kzmijews/8bit-comp/design/clock/schema/ne555n-astable.png

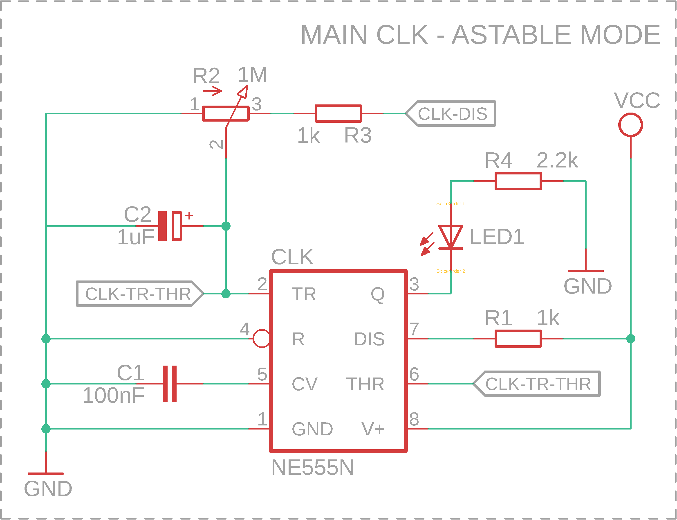
design/clock/schema/ne555n-astable.png
