kzmijews/8bit-comp/design/display/imgs/display-decode-array.png

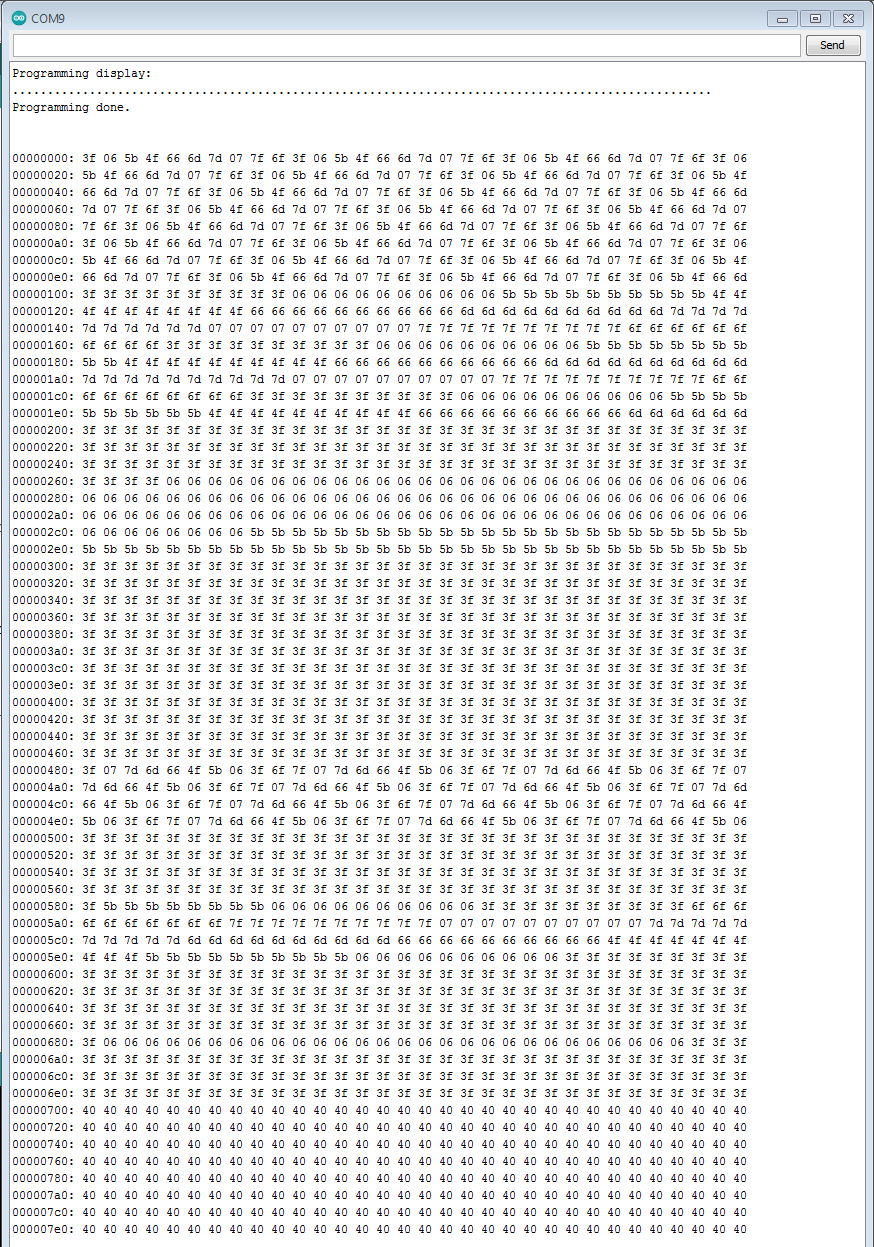
design/display/imgs/display-decode-array.png
