kzmijews/8bit-comp/rel-8bit-computer.pdf

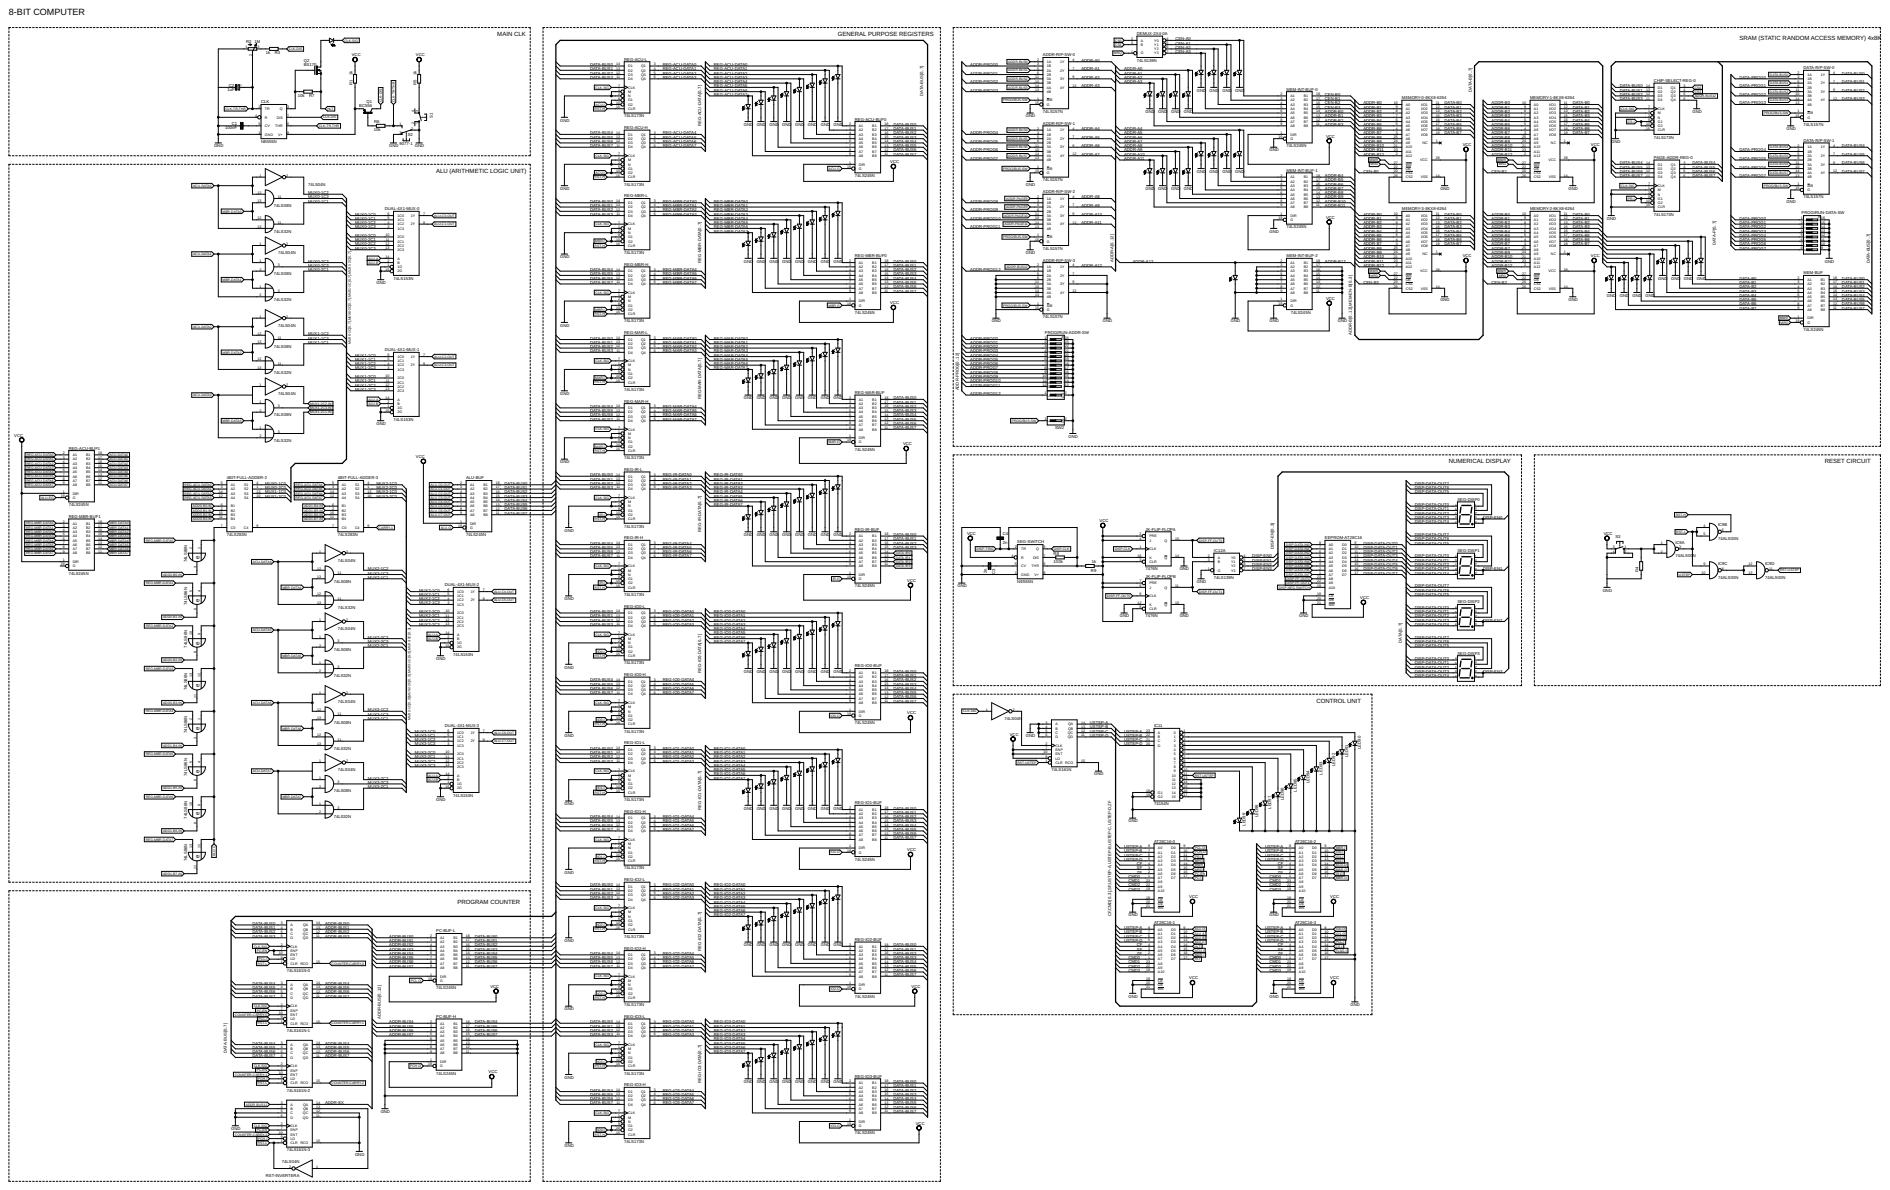
[picture p22: page 1]

SRAM (STATIC RANDOM ACCESS MEMORY) 4x8K

GND GND

GND GND GND GND

ALU (ARITHMETIC LOGIC UNIT)

PROG/RUN-DATA-SW

REG-MBR-DATA[0..7] REG-M

AR-DATA[0..7] REG-IR-DATA[0..7] REG-IO0-DATA[0..7] REG-IO1-DATA[0..7] REG-IO2-DATA[0..7] REG-IO3-DATA[0..7]

REG-ACU-DATA0
REG-ACU-DATA1
REG-ACU-DATA2
REG-ACU-DATA3
REG-ACU-DATA4
REG-ACU-DATA5
REG-ACU-DATA6
REG-ACU-DATA7

ALU-C7-OUT ALU-EO

REG-MBR-DATA0
REG-MBR-DATA1
REG-MBR-DATA2
REG-MBR-DATA3

DISP-DATA-IN0 DISP-DATA-IN1 DISP-DATA-IN2 DISP-DATA-IN3 DISP-DATA-IN4 DISP-DATA-IN5 DISP-DATA-IN6 DISP-DATA-IN7

DATA-IR0 DATA-IR1 DATA-IR2 DATA-IR3

CF,CMD[0..3],SF,USTEP-A,USTEP-B,USTEP-C,USTEP-D,ZF
