kzmijews/8bit-comp/design/ram/schema/rel-ram-8x2K.pdf

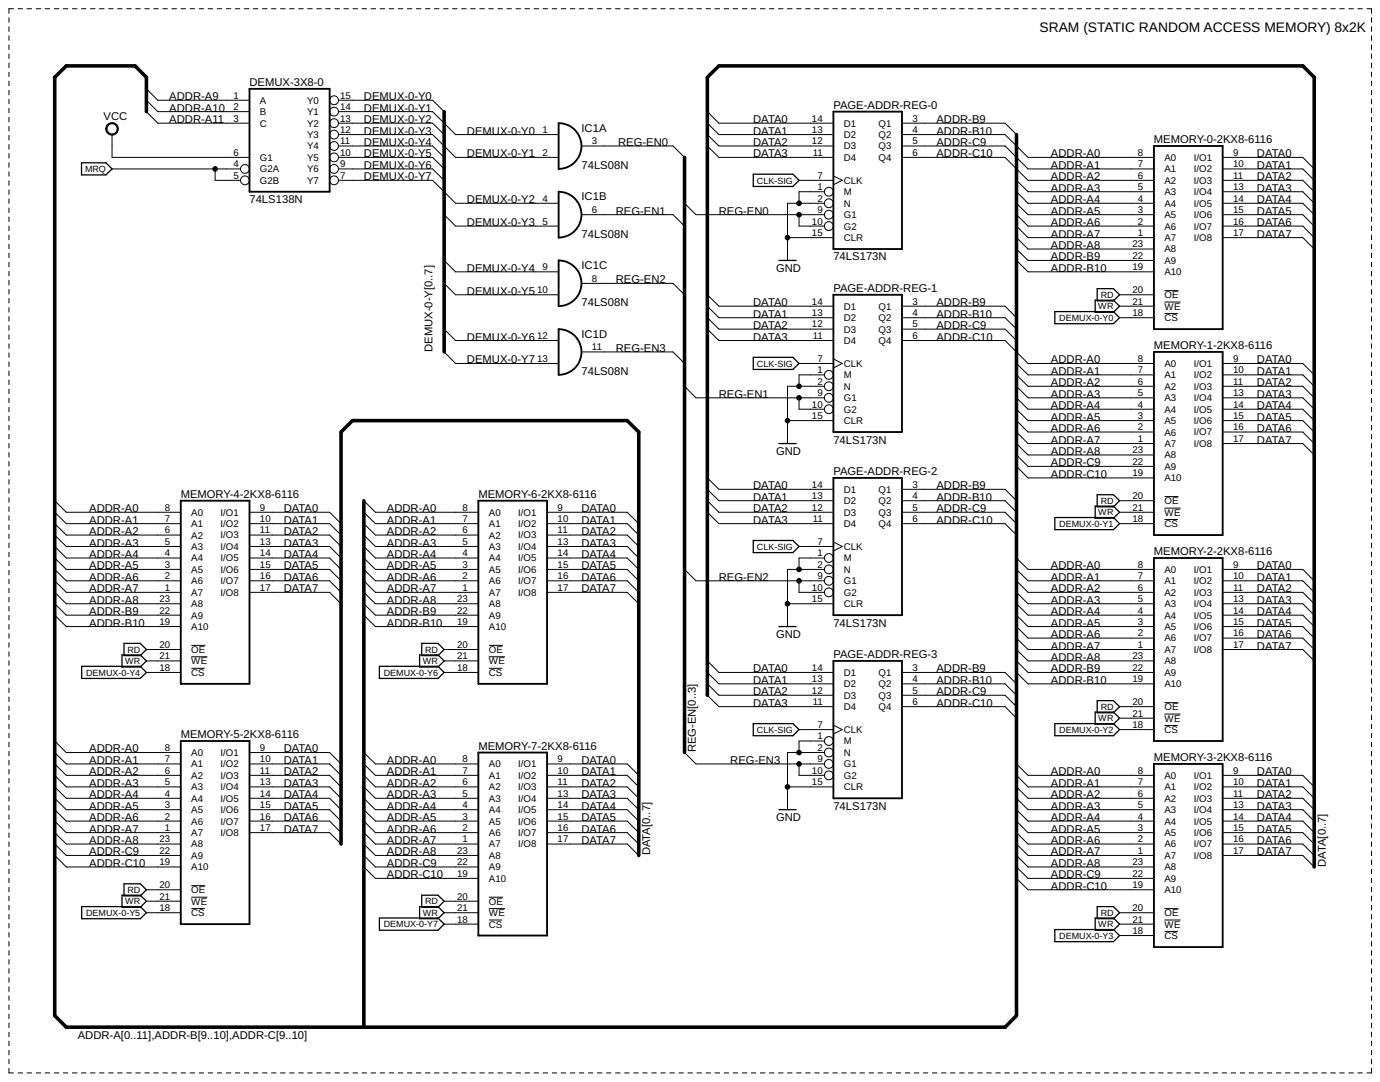
[picture p35: page 1]

SRAM (STATIC RANDOM ACCESS MEMORY) 8x2K
