kzmijews/8bit-comp/design/clock/ltspice/ne555n-monostable-debouncing/ne555n-monostable-debouncing.asc

A1: srflop; Vhigh=4.9V Vlow=0V
C3: cap; 0.1µ; V=10 Irms=2.4 Rser=0.0421193 Lser=0
C4: cap; 10n
D1: LED; NSSW008CT-P1
Q1: npn
R5: res; 100R
R6: res; 1K
R6: res; 2R
R7: res; 1000K
Rt1: res; 5K
Rt2: res; 5K
Rt3: res; 5K
S1: sw
U1: LT1720
U2: LT1720
V1: voltage; 5
V2: voltage; PULSE(0 5 0.1 0 0.01 0.01 0.01 2)
Named nets: 0, THR, Q, set, reset, TRG, CTRL
.tran 1
.model SW SW(RON=.1 ROFF=1GIG VT=4)
DBG_BUTTOM
STEPPING CLK
