kzmijews/8bit-comp/ltspice/debouncing_circuit_timer555_monostable/debouncing_circuit_timer555_monostable.asc

A1: srflop; Vhigh=5V Vlow=0V
C1: cap; 0.1µ; V=10 Irms=2.4 Rser=0.0421193 Lser=0
C2: cap; 10n
D1: LED; NSSW008CT-P1
Q1: npn
R1: res; 5K
R2: res; 5K
R3: res; 5K
R4: res; 1000K
R5: res; 1K
R6: res; 2R
R7: res; 100R
S1: sw
U1: LT1720
U2: LT1720
V1: voltage; 5
V2: voltage; PULSE(0 5 0.1 0 0 0.01)
Named nets: 0, THR, Q, set, reset, TRG, CTRL
.tran 1
.model SW SW(RON=.1 ROFF=1GIG VT=4)
