kzmijews/8bit-comp/design/alu/schema/rel-2b-alu.sch

## EAGLE design design/alu/schema/rel-2b-alu.sch (2024-04-11)

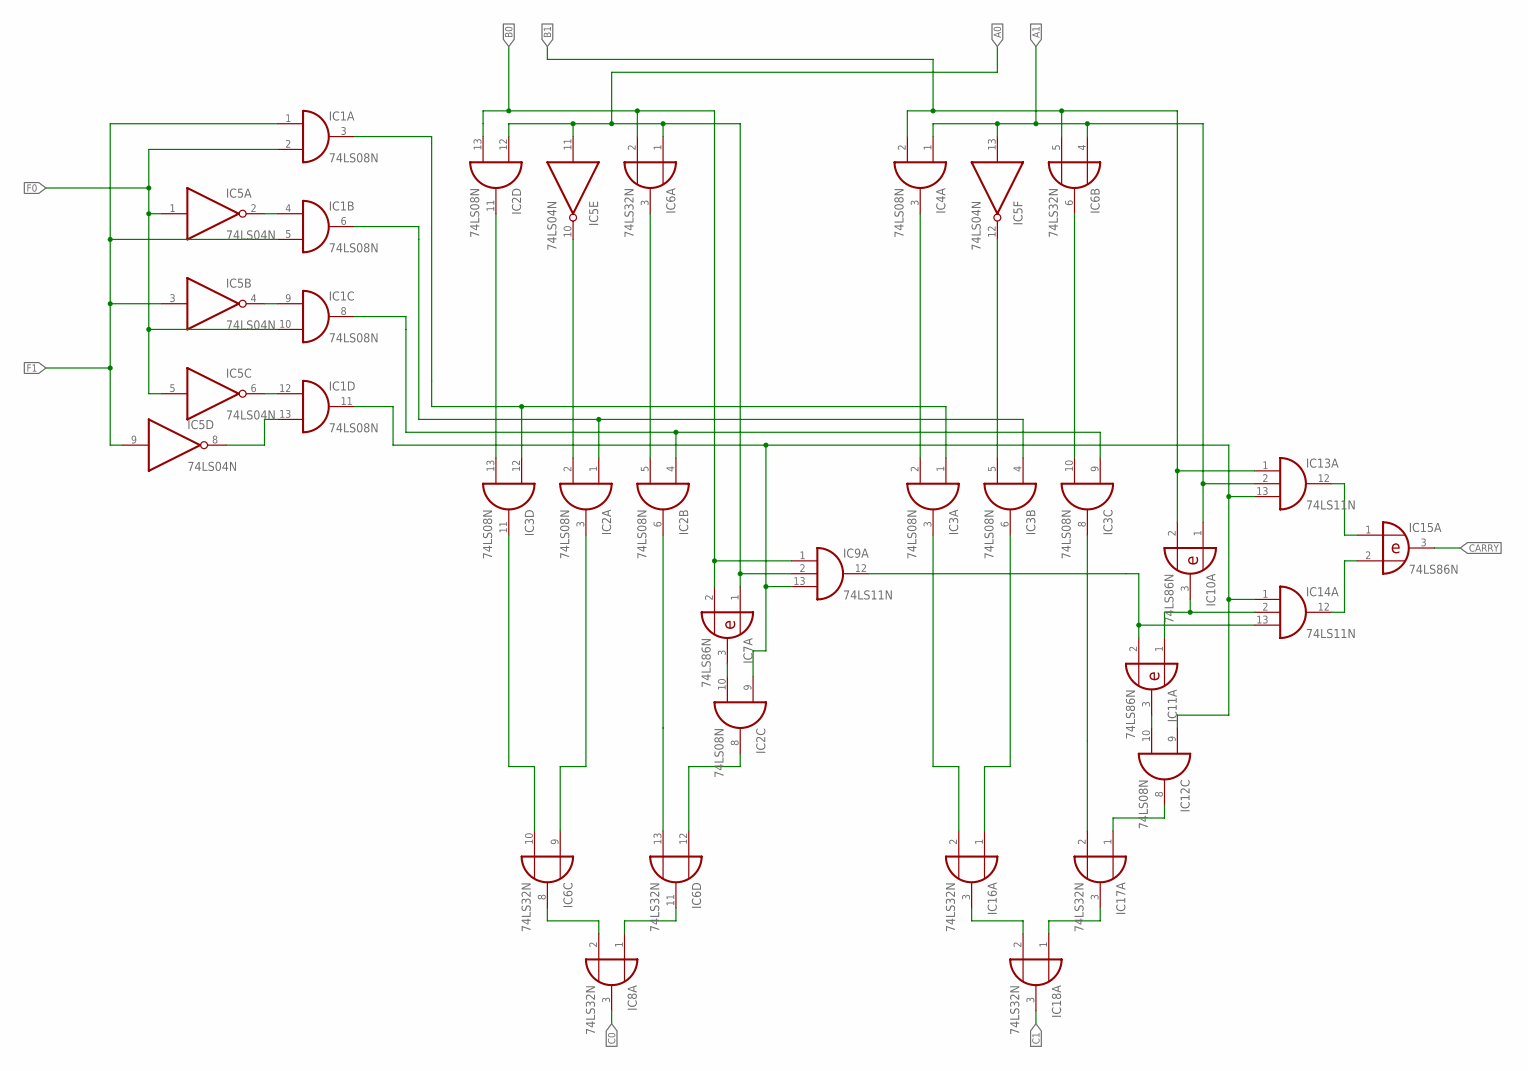
[picture p43: schematic rel-2b-alu.sch]

Parts:
IC1, IC2, IC3, IC4, IC12: 74LS08N; DIL14
IC5: 74LS04N; DIL14
IC6, IC8, IC16, IC17, IC18: 74LS32N; DIL14
IC7, IC10, IC11, IC15: 74LS86N; DIL14
IC9, IC13, IC14: 74LS11N; DIL14

Connections:
A0: IC2.12 (I0), IC5.11 (I), IC6.1 (I0), IC7.1 (I0), IC9.2 (I1)
A1: IC4.1 (I0), IC5.13 (I), IC6.4 (I0), IC10.1 (I0), IC13.2 (I1)
B0: IC2.13 (I1), IC6.2 (I1), IC7.2 (I1), IC9.1 (I0)
B1: IC4.2 (I1), IC6.5 (I1), IC10.2 (I1), IC13.1 (I0)
C0: IC8.3 (O)
C1: IC18.3 (O)
CARRY: IC15.3 (O)
F0: IC1.2 (I1), IC1.10 (I1), IC5.1 (I), IC5.5 (I)
F1: IC1.1 (I0), IC1.5 (I1), IC5.3 (I), IC5.9 (I)
unnamed: IC1.4 (I0), IC5.2 (O)
unnamed: IC1.9 (I0), IC5.4 (O)
unnamed: IC1.12 (I0), IC5.6 (O)
unnamed: IC1.3 (O), IC3.1 (I0), IC3.12 (I0)
unnamed: IC1.6 (O), IC2.1 (I0), IC3.4 (I0)
unnamed: IC1.13 (I1), IC5.8 (O)
unnamed: IC1.8 (O), IC2.4 (I0), IC3.9 (I0)
unnamed: IC1.11 (O), IC2.9 (I0), IC9.13 (I2), IC12.9 (I0), IC13.13 (I2), IC14.1 (I0)
unnamed: IC2.11 (O), IC3.13 (I1)
unnamed: IC2.2 (I1), IC5.10 (O)
unnamed: IC2.5 (I1), IC6.3 (O)
unnamed: IC3.2 (I1), IC4.3 (O)
unnamed: IC3.5 (I1), IC5.12 (O)
unnamed: IC3.10 (I1), IC6.6 (O)
unnamed: IC2.10 (I1), IC7.3 (O)
unnamed: IC3.11 (O), IC6.10 (I1)
unnamed: IC2.3 (O), IC6.9 (I0)
unnamed: IC2.6 (O), IC6.13 (I1)
unnamed: IC2.8 (O), IC6.12 (I0)
unnamed: IC6.8 (O), IC8.2 (I1)
unnamed: IC6.11 (O), IC8.1 (I0)
unnamed: IC10.3 (O), IC11.1 (I0), IC14.2 (I1)
unnamed: IC9.12 (O), IC11.2 (I1), IC14.13 (I2)
unnamed: IC3.3 (O), IC16.2 (I1)
unnamed: IC3.6 (O), IC16.1 (I0)
unnamed: IC3.8 (O), IC17.2 (I1)
unnamed: IC11.3 (O), IC12.10 (I1)
unnamed: IC13.12 (O), IC15.1 (I0)
unnamed: IC14.12 (O), IC15.2 (I1)
unnamed: IC12.8 (O), IC17.1 (I0)
unnamed: IC16.3 (O), IC18.2 (I1)
unnamed: IC17.3 (O), IC18.1 (I0)
