kzmijews/8bit-comp/design/alu/schema/rel-alu.sch

## EAGLE design design/alu/schema/rel-alu.sch (2024-11-08)

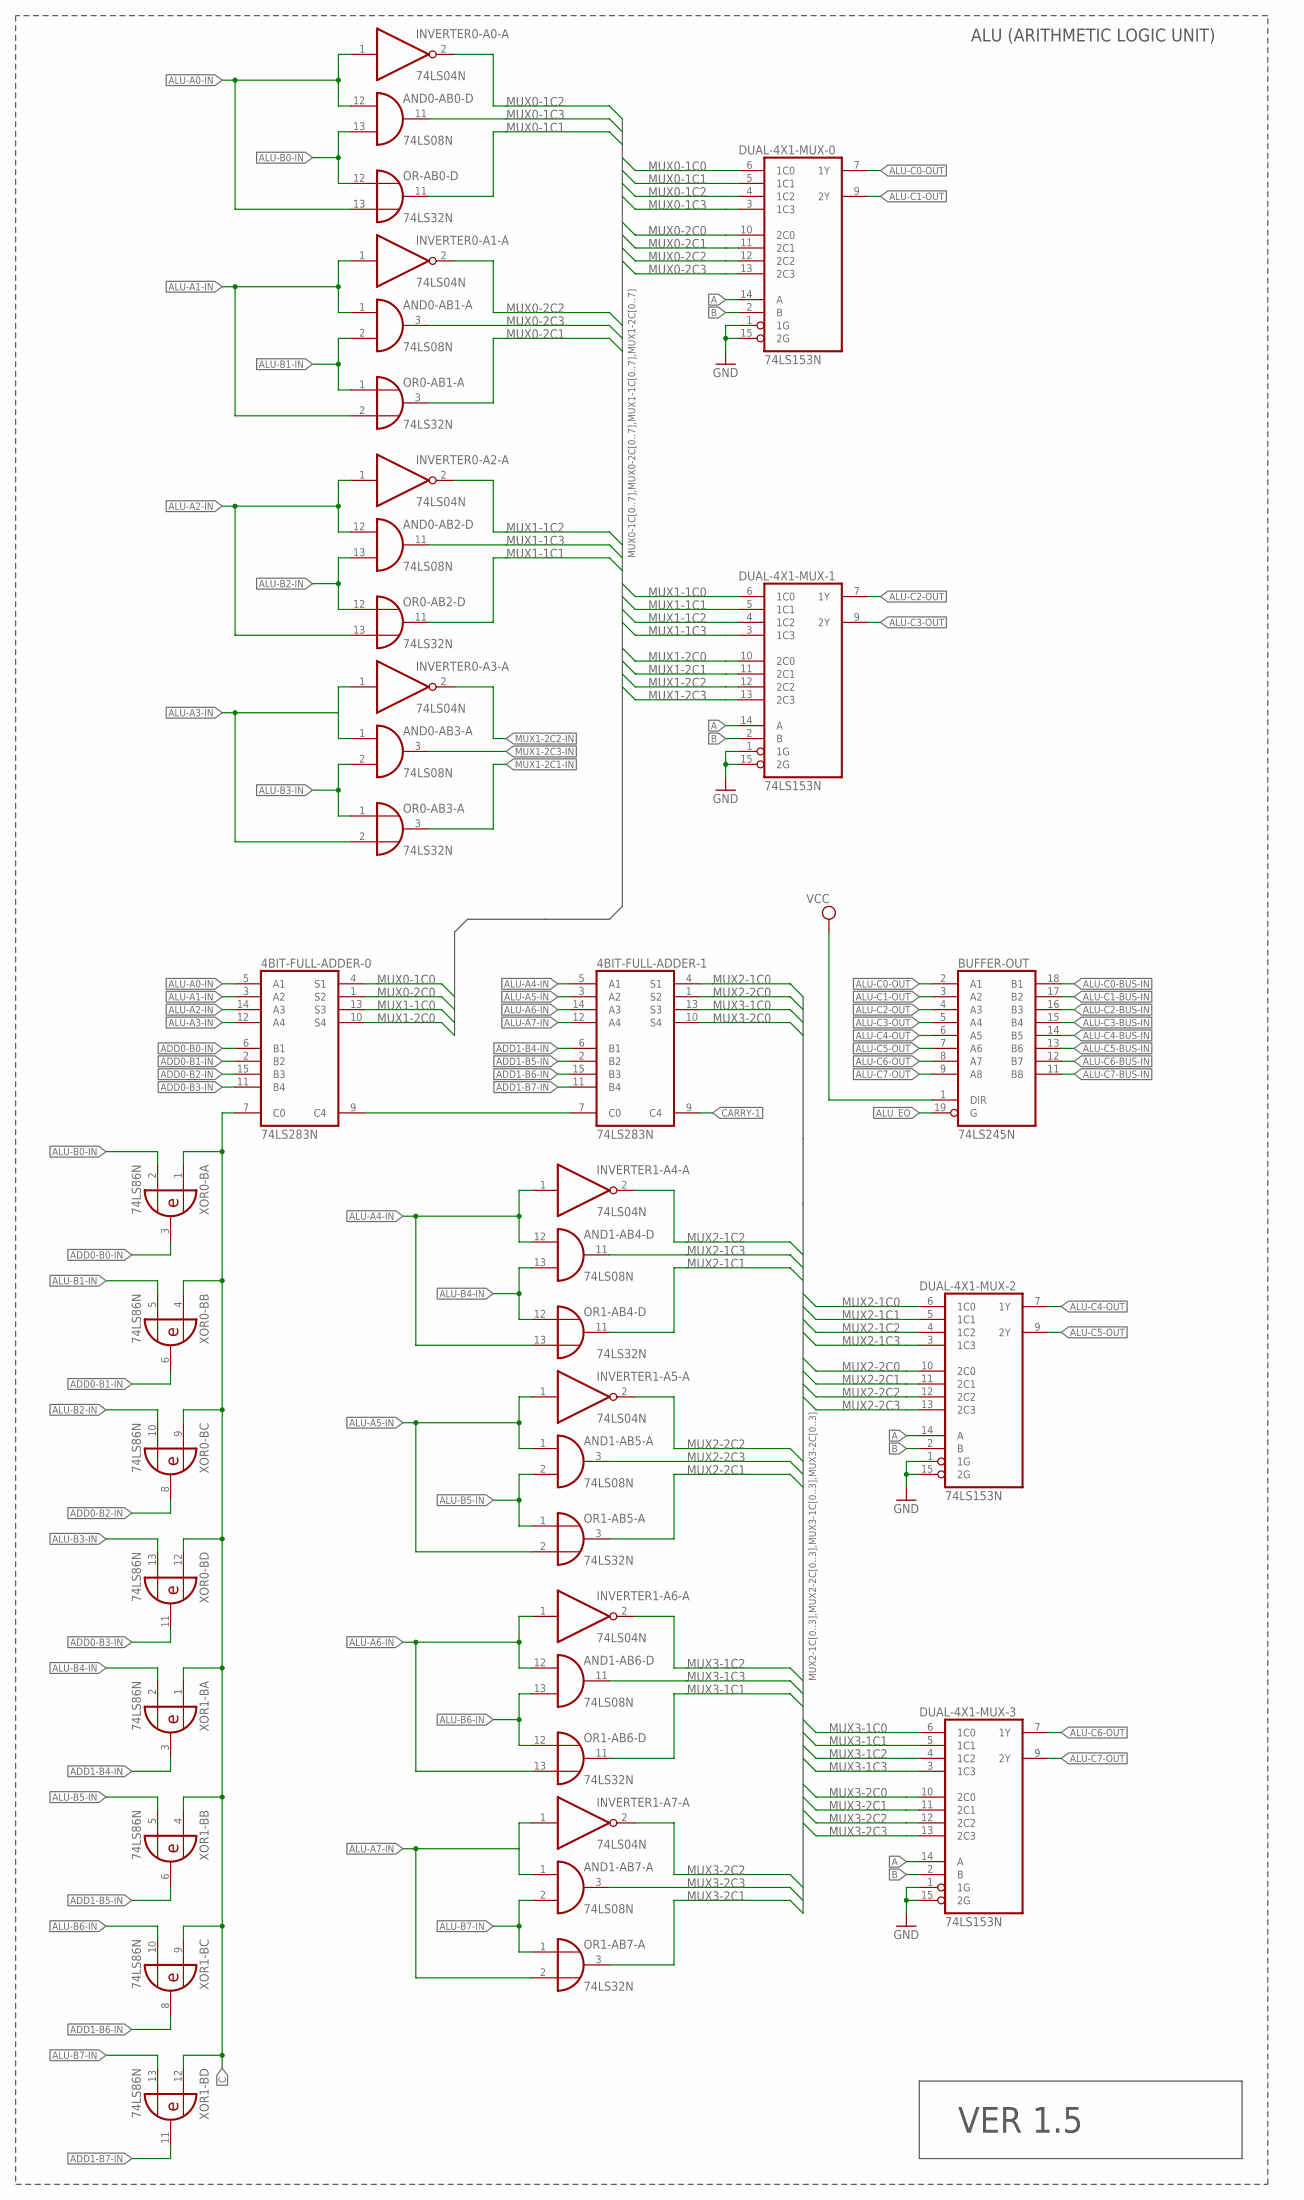
[picture p44: schematic rel-alu.sch]

Parts:
4BIT-FULL-ADDER-0, 4BIT-FULL-ADDER-1: 74LS283N; DIL16
AND0-AB0-, AND0-AB1-, AND0-AB2-, AND0-AB3-, AND1-AB4-, AND1-AB5-, AND1-AB6-, AND1-AB7-: 74LS08N; DIL14
BUFFER-OUT: 74LS245N; DIL20
DUAL-4X1-MUX-0, DUAL-4X1-MUX-1, DUAL-4X1-MUX-2, DUAL-4X1-MUX-3: 74LS153N; DIL16
INVERTER0-A0-, INVERTER0-A1-, INVERTER0-A2-, INVERTER0-A3-, INVERTER1-A4-, INVERTER1-A5-, INVERTER1-A6-, INVERTER1-A7-: 74LS04N; DIL14
OR0-AB1-, OR0-AB2-, OR0-AB3-, OR1-AB4-, OR1-AB5-, OR1-AB6-, OR1-AB7-: 74LS32N; DIL14
OR-AB0-: 74LS32N; DIL14
XOR0-B, XOR1-B: 74LS86N; DIL14

Connections:
A: DUAL-4X1-MUX-0.14 (A), DUAL-4X1-MUX-1.14 (A), DUAL-4X1-MUX-2.14 (A), DUAL-4X1-MUX-3.14 (A)
ADD0-B0-IN: 4BIT-FULL-ADDER-0.6 (B1), XOR0-B.3 (O)
ADD0-B1-IN: 4BIT-FULL-ADDER-0.2 (B2), XOR0-B.6 (O)
ADD0-B2-IN: 4BIT-FULL-ADDER-0.15 (B3), XOR0-B.8 (O)
ADD0-B3-IN: 4BIT-FULL-ADDER-0.11 (B4), XOR0-B.11 (O)
ADD1-B4-IN: 4BIT-FULL-ADDER-1.6 (B1), XOR1-B.3 (O)
ADD1-B5-IN: 4BIT-FULL-ADDER-1.2 (B2), XOR1-B.6 (O)
ADD1-B6-IN: 4BIT-FULL-ADDER-1.15 (B3), XOR1-B.8 (O)
ADD1-B7-IN: 4BIT-FULL-ADDER-1.11 (B4), XOR1-B.11 (O)
ALU-A0-IN: 4BIT-FULL-ADDER-0.5 (A1), AND0-AB0-.12 (I0), INVERTER0-A0-.1 (I), OR-AB0-.13 (I1)
ALU-A1-IN: 4BIT-FULL-ADDER-0.3 (A2), AND0-AB1-.1 (I0), INVERTER0-A1-.1 (I), OR0-AB1-.2 (I1)
ALU-A2-IN: 4BIT-FULL-ADDER-0.14 (A3), AND0-AB2-.12 (I0), INVERTER0-A2-.1 (I), OR0-AB2-.13 (I1)
ALU-A3-IN: 4BIT-FULL-ADDER-0.12 (A4), AND0-AB3-.1 (I0), INVERTER0-A3-.1 (I), OR0-AB3-.2 (I1)
ALU-A4-IN: 4BIT-FULL-ADDER-1.5 (A1), AND1-AB4-.12 (I0), INVERTER1-A4-.1 (I), OR1-AB4-.13 (I1)
ALU-A5-IN: 4BIT-FULL-ADDER-1.3 (A2), AND1-AB5-.1 (I0), INVERTER1-A5-.1 (I), OR1-AB5-.2 (I1)
ALU-A6-IN: 4BIT-FULL-ADDER-1.14 (A3), AND1-AB6-.12 (I0), INVERTER1-A6-.1 (I), OR1-AB6-.13 (I1)
ALU-A7-IN: 4BIT-FULL-ADDER-1.12 (A4), AND1-AB7-.1 (I0), INVERTER1-A7-.1 (I), OR1-AB7-.2 (I1)
ALU-B0-IN: AND0-AB0-.13 (I1), OR-AB0-.12 (I0), XOR0-B.2 (I1)
ALU-B1-IN: AND0-AB1-.2 (I1), OR0-AB1-.1 (I0), XOR0-B.5 (I1)
ALU-B2-IN: AND0-AB2-.13 (I1), OR0-AB2-.12 (I0), XOR0-B.10 (I1)
ALU-B3-IN: AND0-AB3-.2 (I1), OR0-AB3-.1 (I0), XOR0-B.13 (I1)
ALU-B4-IN: AND1-AB4-.13 (I1), OR1-AB4-.12 (I0), XOR1-B.2 (I1)
ALU-B5-IN: AND1-AB5-.2 (I1), OR1-AB5-.1 (I0), XOR1-B.5 (I1)
ALU-B6-IN: AND1-AB6-.13 (I1), OR1-AB6-.12 (I0), XOR1-B.10 (I1)
ALU-B7-IN: AND1-AB7-.2 (I1), OR1-AB7-.1 (I0), XOR1-B.13 (I1)
ALU-C0-BUS-IN: BUFFER-OUT.18 (B1)
ALU-C0-OUT: BUFFER-OUT.2 (A1), DUAL-4X1-MUX-0.7 (1Y)
ALU-C1-BUS-IN: BUFFER-OUT.17 (B2)
ALU-C1-OUT: BUFFER-OUT.3 (A2), DUAL-4X1-MUX-0.9 (2Y)
ALU-C2-BUS-IN: BUFFER-OUT.16 (B3)
ALU-C2-OUT: BUFFER-OUT.4 (A3), DUAL-4X1-MUX-1.7 (1Y)
ALU-C3-BUS-IN: BUFFER-OUT.15 (B4)
ALU-C3-OUT: BUFFER-OUT.5 (A4), DUAL-4X1-MUX-1.9 (2Y)
ALU-C4-BUS-IN: BUFFER-OUT.14 (B5)
ALU-C4-OUT: BUFFER-OUT.6 (A5), DUAL-4X1-MUX-2.7 (1Y)
ALU-C5-BUS-IN: BUFFER-OUT.13 (B6)
ALU-C5-OUT: BUFFER-OUT.7 (A6), DUAL-4X1-MUX-2.9 (2Y)
ALU-C6-BUS-IN: BUFFER-OUT.12 (B7)
ALU-C6-OUT: BUFFER-OUT.8 (A7), DUAL-4X1-MUX-3.7 (1Y)
ALU-C7-BUS-IN: BUFFER-OUT.11 (B8)
ALU-C7-OUT: BUFFER-OUT.9 (A8), DUAL-4X1-MUX-3.9 (2Y)
ALU_EO: BUFFER-OUT.19 (G)
B: DUAL-4X1-MUX-0.2 (B), DUAL-4X1-MUX-1.2 (B), DUAL-4X1-MUX-2.2 (B), DUAL-4X1-MUX-3.2 (B)
C: 4BIT-FULL-ADDER-0.7 (C0), XOR0-B.1 (I0), XOR0-B.4 (I0), XOR0-B.9 (I0), XOR0-B.12 (I0), XOR1-B.1 (I0), XOR1-B.4 (I0), XOR1-B.9 (I0), XOR1-B.12 (I0)
CARRY-1: 4BIT-FULL-ADDER-1.9 (C4)
GND: DUAL-4X1-MUX-0.1 (1G), DUAL-4X1-MUX-0.15 (2G), DUAL-4X1-MUX-1.1 (1G), DUAL-4X1-MUX-1.15 (2G), DUAL-4X1-MUX-2.1 (1G), DUAL-4X1-MUX-2.15 (2G), DUAL-4X1-MUX-3.1 (1G), DUAL-4X1-MUX-3.15 (2G)
MUX0-1C0: 4BIT-FULL-ADDER-0.4 (S1), DUAL-4X1-MUX-0.6 (1C0)
MUX0-1C1: DUAL-4X1-MUX-0.5 (1C1), OR-AB0-.11 (O)
MUX0-1C2: DUAL-4X1-MUX-0.4 (1C2), INVERTER0-A0-.2 (O)
MUX0-1C3: AND0-AB0-.11 (O), DUAL-4X1-MUX-0.3 (1C3)
MUX0-2C0: 4BIT-FULL-ADDER-0.1 (S2), DUAL-4X1-MUX-0.10 (2C0)
MUX0-2C1: DUAL-4X1-MUX-0.11 (2C1), OR0-AB1-.3 (O)
MUX0-2C2: DUAL-4X1-MUX-0.12 (2C2), INVERTER0-A1-.2 (O)
MUX0-2C3: AND0-AB1-.3 (O), DUAL-4X1-MUX-0.13 (2C3)
MUX1-1C0: 4BIT-FULL-ADDER-0.13 (S3), DUAL-4X1-MUX-1.6 (1C0)
MUX1-1C1: DUAL-4X1-MUX-1.5 (1C1), OR0-AB2-.11 (O)
MUX1-1C2: DUAL-4X1-MUX-1.4 (1C2), INVERTER0-A2-.2 (O)
MUX1-1C3: AND0-AB2-.11 (O), DUAL-4X1-MUX-1.3 (1C3)
MUX1-2C0: 4BIT-FULL-ADDER-0.10 (S4), DUAL-4X1-MUX-1.10 (2C0)
MUX1-2C1: DUAL-4X1-MUX-1.11 (2C1)
MUX1-2C1-IN: OR0-AB3-.3 (O)
MUX1-2C2: DUAL-4X1-MUX-1.12 (2C2)
MUX1-2C2-IN: INVERTER0-A3-.2 (O)
MUX1-2C3: DUAL-4X1-MUX-1.13 (2C3)
MUX1-2C3-IN: AND0-AB3-.3 (O)
MUX2-1C0: 4BIT-FULL-ADDER-1.4 (S1), DUAL-4X1-MUX-2.6 (1C0)
MUX2-1C1: DUAL-4X1-MUX-2.5 (1C1), OR1-AB4-.11 (O)
MUX2-1C2: DUAL-4X1-MUX-2.4 (1C2), INVERTER1-A4-.2 (O)
MUX2-1C3: AND1-AB4-.11 (O), DUAL-4X1-MUX-2.3 (1C3)
MUX2-2C0: 4BIT-FULL-ADDER-1.1 (S2), DUAL-4X1-MUX-2.10 (2C0)
MUX2-2C1: DUAL-4X1-MUX-2.11 (2C1), OR1-AB5-.3 (O)
MUX2-2C2: DUAL-4X1-MUX-2.12 (2C2), INVERTER1-A5-.2 (O)
MUX2-2C3: AND1-AB5-.3 (O), DUAL-4X1-MUX-2.13 (2C3)
MUX3-1C0: 4BIT-FULL-ADDER-1.13 (S3), DUAL-4X1-MUX-3.6 (1C0)
MUX3-1C1: DUAL-4X1-MUX-3.5 (1C1), OR1-AB6-.11 (O)
MUX3-1C2: DUAL-4X1-MUX-3.4 (1C2), INVERTER1-A6-.2 (O)
MUX3-1C3: AND1-AB6-.11 (O), DUAL-4X1-MUX-3.3 (1C3)
MUX3-2C0: 4BIT-FULL-ADDER-1.10 (S4), DUAL-4X1-MUX-3.10 (2C0)
MUX3-2C1: DUAL-4X1-MUX-3.11 (2C1), OR1-AB7-.3 (O)
MUX3-2C2: DUAL-4X1-MUX-3.12 (2C2), INVERTER1-A7-.2 (O)
MUX3-2C3: AND1-AB7-.3 (O), DUAL-4X1-MUX-3.13 (2C3)
unnamed: 4BIT-FULL-ADDER-0.9 (C4), 4BIT-FULL-ADDER-1.7 (C0)
VCC: BUFFER-OUT.1 (DIR)

Notes on the sheet:
ALU (ARITHMETIC LOGIC UNIT)
VER 1.5
