kzmijews/8bit-comp/design/clock/schema/ne555n-astable.sch

## EAGLE design design/clock/schema/ne555n-astable.sch (2023-10-19)

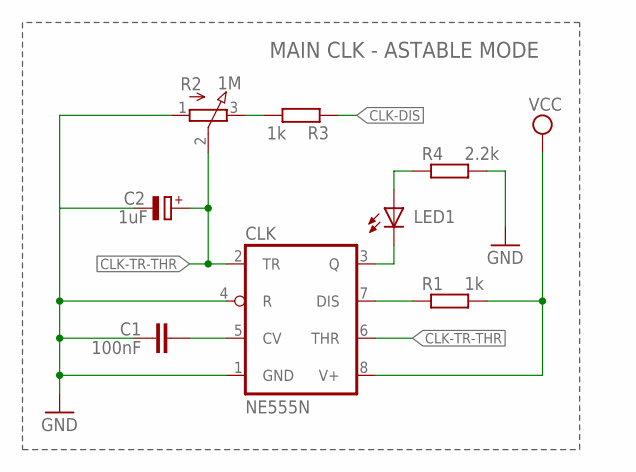
[picture p45: schematic ne555n-astable.sch]

Parts:
C1: 100nF; C025-050X050
C2: 1uF; E2-5
CLK: NE555N; DIL08
LED1: LED_ELD260; LED_LD260
R1, R3: 1k; 0204/5
R2: 1M; 3RP/1610N
R4: 2.2k; 0204/5

Connections:
CLK-CV: C1.2, CLK.5 (CV)
CLK-DIS: CLK.7 (DIS), R1.1, R3.1
CLK-Q: CLK.3 (Q), LED1.K (C)
CLK-TR-THR: C2.+, CLK.2 (TR), CLK.6 (THR), R2.2 (S)
GND: C1.1, C2.-, CLK.1 (GND), CLK.4 (R), R2.1 (A), R4.2
unnamed: R2.3 (E), R3.2
unnamed: LED1.A, R4.1
VCC: CLK.8 (V+), R1.2

Notes on the sheet:
MAIN CLK - ASTABLE MODE
