kzmijews/8bit-comp/design/clock/schema/ne555n-monostable.sch

## EAGLE design design/clock/schema/ne555n-monostable.sch (2023-10-19)

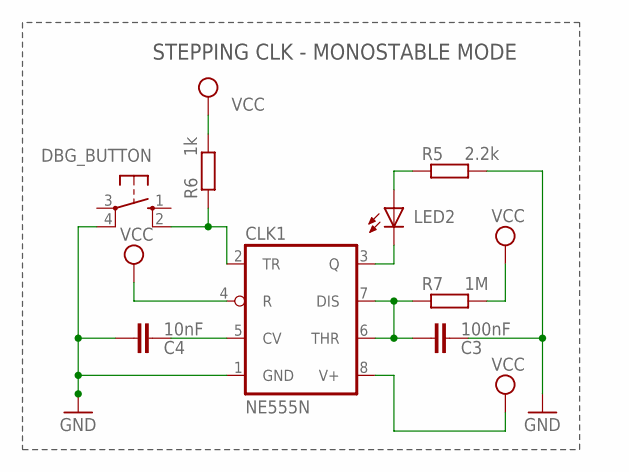
[picture p46: schematic ne555n-monostable.sch]

Parts:
C3: 100nF; C025-050X050
C4: 10nF; C025-050X050
CLK1: NE555N; DIL08
DBG_BUTTON: 10-XX; B3F-10XX
LED2: LED_ELD260; LED_LD260
R5: 2.2k; 0204/5
R6: 1k; 0204/5
R7: 1M; 0204/5

Connections:
GND: C3.1, C4.2, CLK1.1 (GND), DBG_BUTTON.4 (P1), R5.2
unnamed: CLK1.3 (Q), LED2.K (C)
unnamed: LED2.A, R5.1
unnamed: CLK1.2 (TR), DBG_BUTTON.2 (S1), R6.1
unnamed: C3.2, CLK1.6 (THR), CLK1.7 (DIS), R7.1
unnamed: C4.1, CLK1.5 (CV)
VCC: CLK1.4 (R), CLK1.8 (V+), R6.2, R7.2

Notes on the sheet:
STEPPING CLK - MONOSTABLE MODE
