kzmijews/8bit-comp/design/clock/schema/rel-clock.sch

## EAGLE design design/clock/schema/rel-clock.sch (2024-07-01)

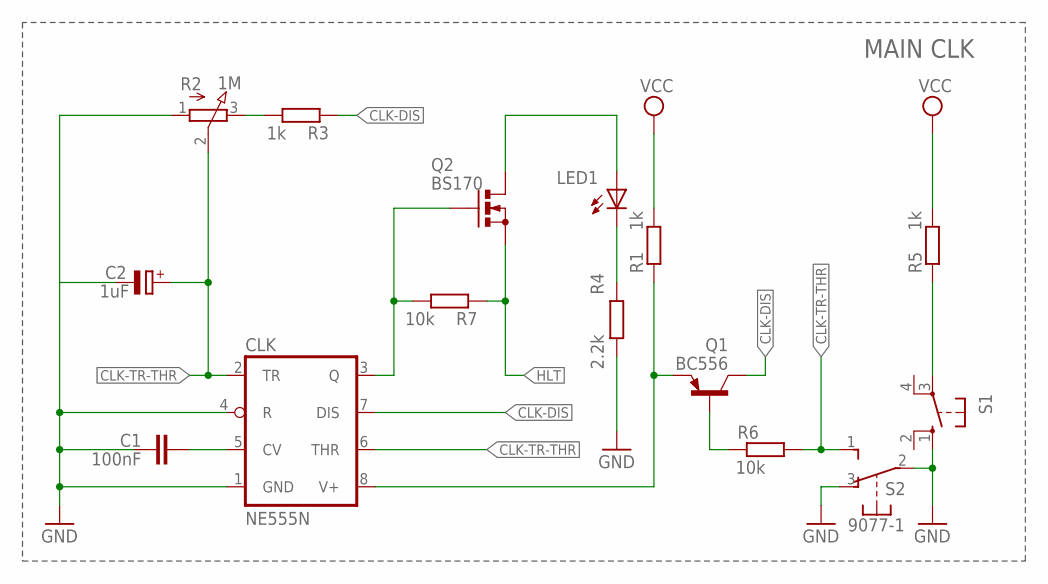
[picture p47: schematic rel-clock.sch]

Parts:
C1: 100nF; C025-050X050
C2: 1uF; E2-5
CLK: NE555N; DIL08
LED1: LED_ELD260; LED_LD260
Q1: BC556; TO92-EBC
Q2: BS170; SOT54E
R1, R3, R5: 1k; 0204/5
R2: 1M; 3RP/1610N
R4: 2.2k; 0204/5
R6, R7: 10k; 0204/5
S1: 10-XX; B3F-10XX
S2: 9077-1

Connections:
CLK-CV: C1.2, CLK.5 (CV)
CLK-DIS: CLK.7 (DIS), Q1.C, R3.1
CLK-TR-THR: C2.+, CLK.2 (TR), CLK.6 (THR), Q1.B, R2.2 (S), R6.1, R6.2, S2.1 (S)
GND: C1.1, C2.-, CLK.1 (GND), CLK.4 (R), R2.1 (A), R4.2, S1.1 (S), S2.2, S2.3 (O)
HLT: Q2.S, R7.1
unnamed: R5.1, S1.3
unnamed: R2.3 (E), R3.2
unnamed: CLK.8 (V+), Q1.E, R1.1
unnamed: LED1.K (C), R4.1
unnamed: LED1.A, Q2.D
Q: CLK.3 (Q), Q2.G, R7.2
VCC: R1.2, R5.2

Notes on the sheet:
MAIN CLK
