kzmijews/8bit-comp/design/cu/schema/rel-cu.sch

## EAGLE design design/cu/schema/rel-cu.sch (2024-11-16)

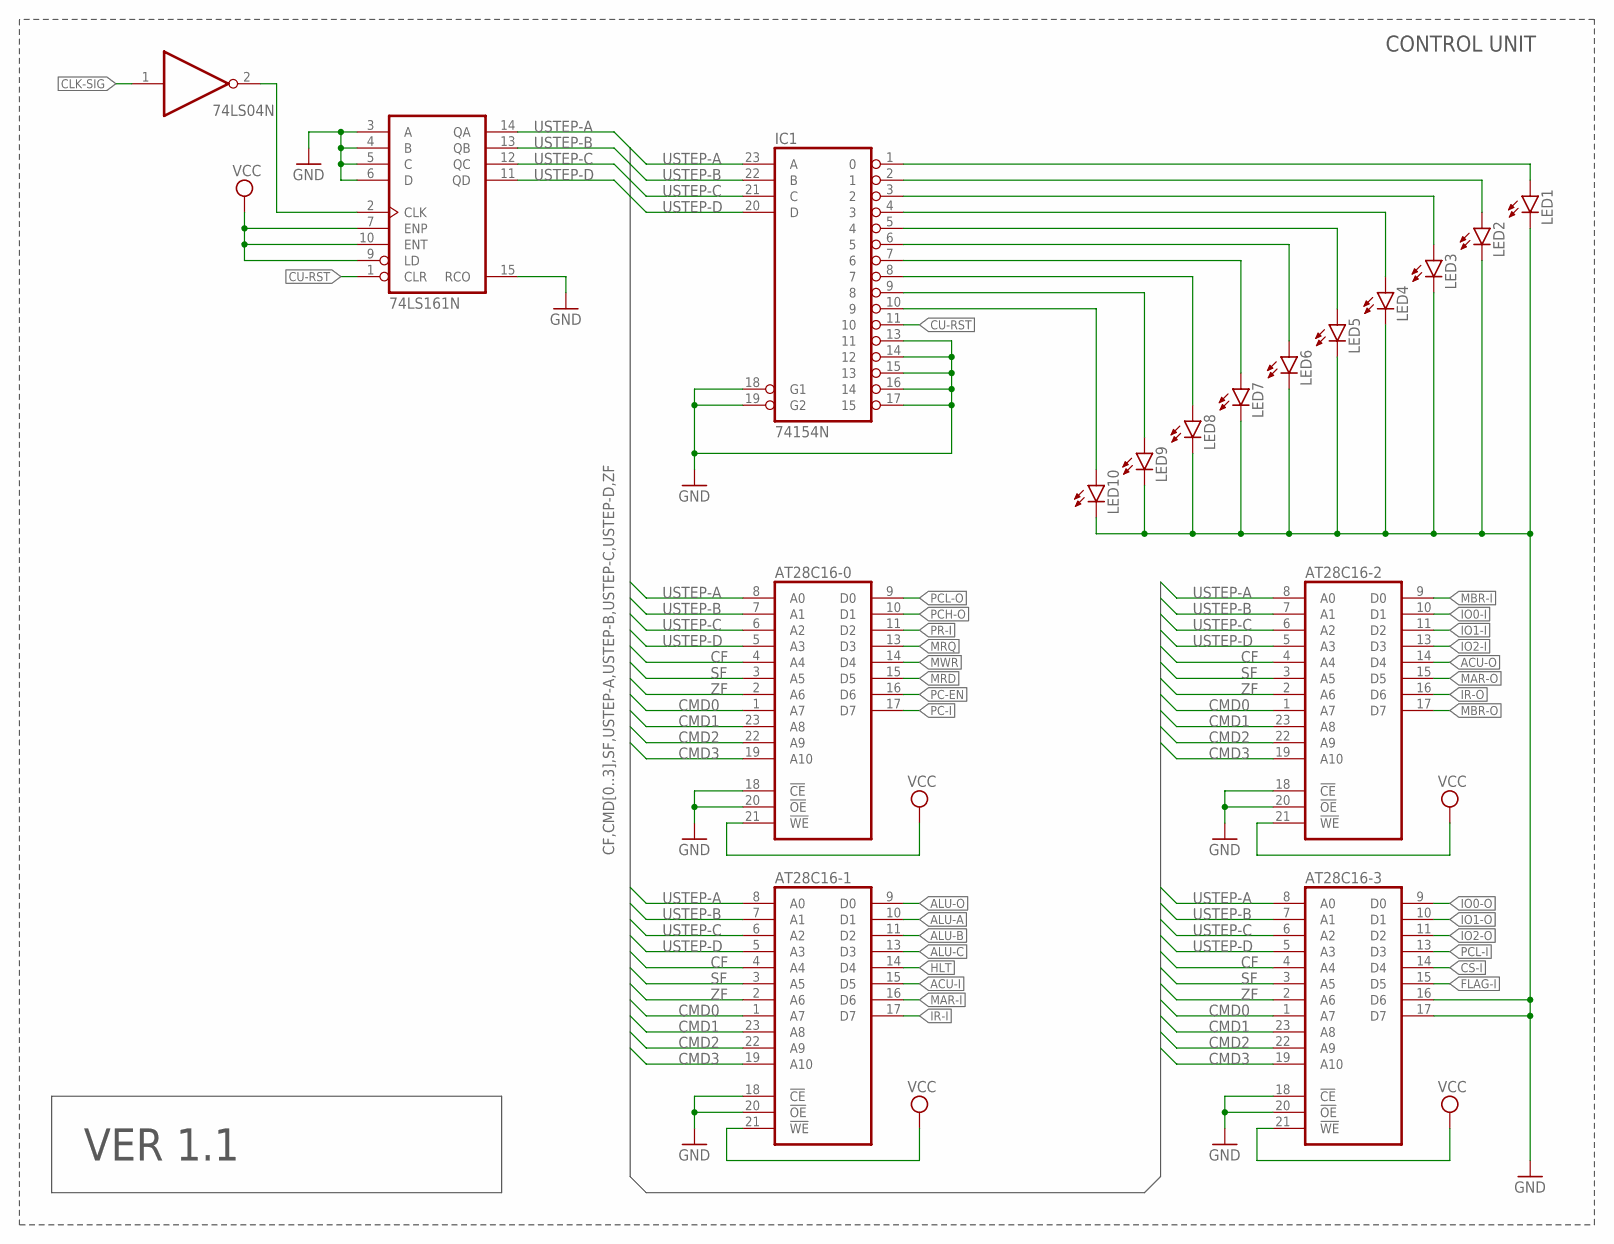
[picture p48: schematic rel-cu.sch]

Parts:
74LS161N: 74160N; DIL16
AT28C16-0, AT28C16-1, AT28C16-2, AT28C16-3: 2816; DIL24
IC1: 74154N; DIL24-6
IC2: 74LS04N; DIL14
LED1, LED2, LED3, LED4, LED5, LED6, LED7, LED8, LED9, LED10: LED5MM

Connections:
ACU-I: AT28C16-1.15 (D5)
ACU-O: AT28C16-2.14 (D4)
ALU-A: AT28C16-1.10 (D1)
ALU-B: AT28C16-1.11 (D2)
ALU-C: AT28C16-1.13 (D3)
ALU-O: AT28C16-1.9 (D0)
CF: AT28C16-0.4 (A4), AT28C16-1.4 (A4), AT28C16-2.4 (A4), AT28C16-3.4 (A4)
CLK-SIG: 74LS161N.2 (CLK), IC2.1 (I), IC2.2 (O)
CMD0: AT28C16-0.1 (A7), AT28C16-1.1 (A7), AT28C16-2.1 (A7), AT28C16-3.1 (A7)
CMD1: AT28C16-0.23 (A8), AT28C16-1.23 (A8), AT28C16-2.23 (A8), AT28C16-3.23 (A8)
CMD2: AT28C16-0.22 (A9), AT28C16-1.22 (A9), AT28C16-2.22 (A9), AT28C16-3.22 (A9)
CMD3: AT28C16-0.19 (A10), AT28C16-1.19 (A10), AT28C16-2.19 (A10), AT28C16-3.19 (A10)
CS-I: AT28C16-3.14 (D4)
CU-RST: 74LS161N.1 (CLR), IC1.11 (10)
FLAG-I: AT28C16-3.15 (D5)
GND: 74LS161N.3 (A), 74LS161N.4 (B), 74LS161N.5 (C), 74LS161N.6 (D), 74LS161N.15 (RCO), AT28C16-0.18 (!CE), AT28C16-0.20 (!OE), AT28C16-1.18 (!CE), AT28C16-1.20 (!OE), AT28C16-2.18 (!CE), AT28C16-2.20 (!OE), AT28C16-3.16 (D6), AT28C16-3.17 (D7), AT28C16-3.18 (!CE), AT28C16-3.20 (!OE), IC1.13 (11), IC1.14 (12), IC1.15 (13), IC1.16 (14), IC1.17 (15), IC1.18 (G1), IC1.19 (G2), LED1.K (C), LED2.K (C), LED3.K (C), LED4.K (C), LED5.K (C), LED6.K (C), LED7.K (C), LED8.K (C), LED9.K (C), LED10.K (C)
HLT: AT28C16-1.14 (D4)
IO0-I: AT28C16-2.10 (D1)
IO0-O: AT28C16-3.9 (D0)
IO1-I: AT28C16-2.11 (D2)
IO1-O: AT28C16-3.10 (D1)
IO2-I: AT28C16-2.13 (D3)
IO2-O: AT28C16-3.11 (D2)
IR-I: AT28C16-1.17 (D7)
IR-O: AT28C16-2.16 (D6)
MAR-I: AT28C16-1.16 (D6)
MAR-O: AT28C16-2.15 (D5)
MBR-I: AT28C16-2.9 (D0)
MBR-O: AT28C16-2.17 (D7)
MRD: AT28C16-0.15 (D5)
MRQ: AT28C16-0.13 (D3)
MWR: AT28C16-0.14 (D4)
unnamed: IC1.1 (0), LED1.A
unnamed: IC1.2 (1), LED2.A
unnamed: IC1.3 (2), LED3.A
unnamed: IC1.4 (3), LED4.A
unnamed: IC1.5 (4), LED5.A
unnamed: IC1.6 (5), LED6.A
unnamed: IC1.7 (6), LED7.A
unnamed: IC1.8 (7), LED8.A
unnamed: IC1.9 (8), LED9.A
unnamed: IC1.10 (9), LED10.A
PC-EN: AT28C16-0.16 (D6)
PC-I: AT28C16-0.17 (D7)
PCH-O: AT28C16-0.10 (D1)
PCL-I: AT28C16-3.13 (D3)
PCL-O: AT28C16-0.9 (D0)
PR-I: AT28C16-0.11 (D2)
SF: AT28C16-0.3 (A5), AT28C16-1.3 (A5), AT28C16-2.3 (A5), AT28C16-3.3 (A5)
USTEP-A: 74LS161N.14 (QA), AT28C16-0.8 (A0), AT28C16-1.8 (A0), AT28C16-2.8 (A0), AT28C16-3.8 (A0), IC1.23 (A)
USTEP-B: 74LS161N.13 (QB), AT28C16-0.7 (A1), AT28C16-1.7 (A1), AT28C16-2.7 (A1), AT28C16-3.7 (A1), IC1.22 (B)
USTEP-C: 74LS161N.12 (QC), AT28C16-0.6 (A2), AT28C16-1.6 (A2), AT28C16-2.6 (A2), AT28C16-3.6 (A2), IC1.21 (C)
USTEP-D: 74LS161N.11 (QD), AT28C16-0.5 (A3), AT28C16-1.5 (A3), AT28C16-2.5 (A3), AT28C16-3.5 (A3), IC1.20 (D)
VCC: 74LS161N.7 (ENP), 74LS161N.9 (LD), 74LS161N.10 (ENT), AT28C16-0.21 (!WE), AT28C16-1.21 (!WE), AT28C16-2.21 (!WE), AT28C16-3.21 (!WE)
ZF: AT28C16-0.2 (A6), AT28C16-1.2 (A6), AT28C16-2.2 (A6), AT28C16-3.2 (A6)

Notes on the sheet:
CONTROL UNIT
VER 1.1
