kzmijews/8bit-comp/design/pc/schema/dbg-prog-counter.sch

## EAGLE design design/pc/schema/dbg-prog-counter.sch (2024-07-01)

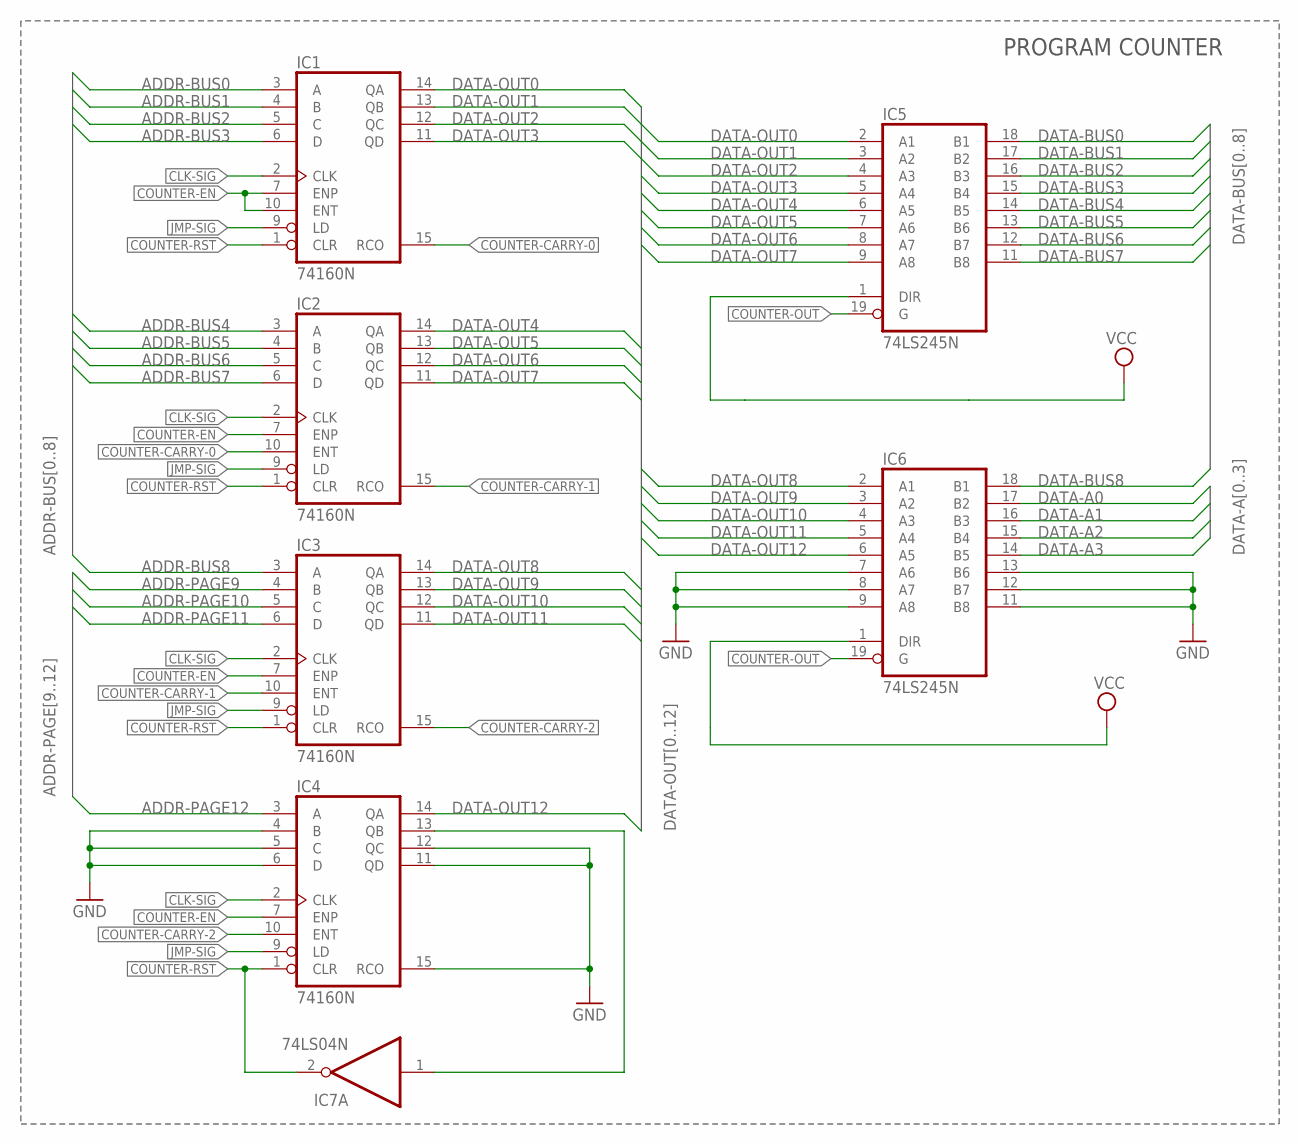
[picture p49: schematic dbg-prog-counter.sch]

Parts:
IC1, IC2, IC3, IC4: 74160N; DIL16
IC5, IC6: 74LS245N; DIL20
IC7: 74LS04N; DIL14

Connections:
ADDR-BUS0: IC1.3 (A)
ADDR-BUS1: IC1.4 (B)
ADDR-BUS2: IC1.5 (C)
ADDR-BUS3: IC1.6 (D)
ADDR-BUS4: IC2.3 (A)
ADDR-BUS5: IC2.4 (B)
ADDR-BUS6: IC2.5 (C)
ADDR-BUS7: IC2.6 (D)
ADDR-BUS8: IC3.3 (A)
ADDR-PAGE9: IC3.4 (B)
ADDR-PAGE10: IC3.5 (C)
ADDR-PAGE11: IC3.6 (D)
ADDR-PAGE12: IC4.3 (A)
CLK-SIG: IC1.2 (CLK), IC2.2 (CLK), IC3.2 (CLK), IC4.2 (CLK)
COUNTER-CARRY-0: IC1.15 (RCO), IC2.10 (ENT)
COUNTER-CARRY-1: IC2.15 (RCO), IC3.10 (ENT)
COUNTER-CARRY-2: IC3.15 (RCO), IC4.10 (ENT)
COUNTER-EN: IC1.7 (ENP), IC1.10 (ENT), IC2.7 (ENP), IC3.7 (ENP), IC4.7 (ENP)
COUNTER-OUT: IC5.19 (G), IC6.19 (G)
COUNTER-RST: IC1.1 (CLR), IC2.1 (CLR), IC3.1 (CLR), IC4.1 (CLR), IC7.2 (O)
DATA-A0: IC6.17 (B2)
DATA-A1: IC6.16 (B3)
DATA-A2: IC6.15 (B4)
DATA-A3: IC6.14 (B5)
DATA-BUS0: IC5.18 (B1)
DATA-BUS1: IC5.17 (B2)
DATA-BUS2: IC5.16 (B3)
DATA-BUS3: IC5.15 (B4)
DATA-BUS4: IC5.14 (B5)
DATA-BUS5: IC5.13 (B6)
DATA-BUS6: IC5.12 (B7)
DATA-BUS7: IC5.11 (B8)
DATA-BUS8: IC6.18 (B1)
DATA-OUT0: IC1.14 (QA), IC5.2 (A1)
DATA-OUT1: IC1.13 (QB), IC5.3 (A2)
DATA-OUT2: IC1.12 (QC), IC5.4 (A3)
DATA-OUT3: IC1.11 (QD), IC5.5 (A4)
DATA-OUT4: IC2.14 (QA), IC5.6 (A5)
DATA-OUT5: IC2.13 (QB), IC5.7 (A6)
DATA-OUT6: IC2.12 (QC), IC5.8 (A7)
DATA-OUT7: IC2.11 (QD), IC5.9 (A8)
DATA-OUT8: IC3.14 (QA), IC6.2 (A1)
DATA-OUT9: IC3.13 (QB), IC6.3 (A2)
DATA-OUT10: IC3.12 (QC), IC6.4 (A3)
DATA-OUT11: IC3.11 (QD), IC6.5 (A4)
DATA-OUT12: IC4.14 (QA), IC6.6 (A5)
GND: IC4.4 (B), IC4.5 (C), IC4.6 (D), IC4.11 (QD), IC4.12 (QC), IC4.15 (RCO), IC6.7 (A6), IC6.8 (A7), IC6.9 (A8), IC6.11 (B8), IC6.12 (B7), IC6.13 (B6)
JMP-SIG: IC1.9 (LD), IC2.9 (LD), IC3.9 (LD), IC4.9 (LD)
unnamed: IC4.13 (QB), IC7.1 (I)
VCC: IC5.1 (DIR), IC6.1 (DIR)

Notes on the sheet:
PROGRAM COUNTER
