kzmijews/8bit-comp/design/reset/schema/rel-reset.sch

## EAGLE design design/reset/schema/rel-reset.sch (2024-11-22)

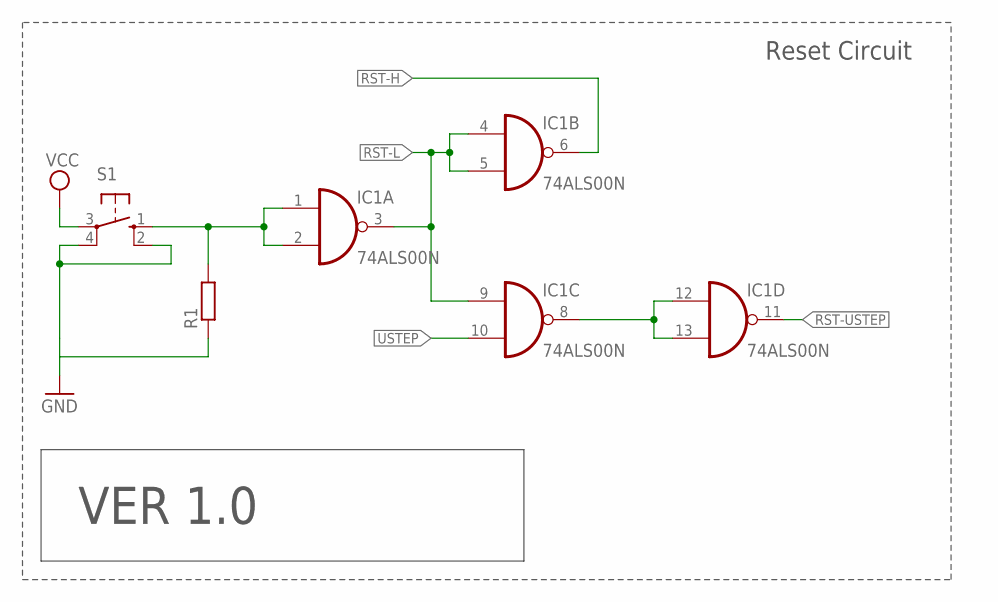
[picture p56: schematic rel-reset.sch]

Parts:
IC1: 74ALS00N; DIL14
R1: R-EU_0204/5; 0204/5
S1: 10-XX; B3F-10XX

Connections:
GND: R1.1, S1.2 (S1), S1.4 (P1)
unnamed: IC1.1 (I0), IC1.2 (I1), R1.2, S1.1 (S)
unnamed: IC1.8 (O), IC1.12 (I0), IC1.13 (I1)
RST-H: IC1.6 (O)
RST-L: IC1.3 (O), IC1.4 (I0), IC1.5 (I1), IC1.9 (I0)
RST-USTEP: IC1.11 (O)
USTEP: IC1.10 (I1)
VCC: S1.3

Notes on the sheet:
Reset Circuit
VER 1.0
