kzmijews/8bit-comp/design/rflag/schema/rel-rflag.sch

## EAGLE design design/rflag/schema/rel-rflag.sch (2024-11-16)

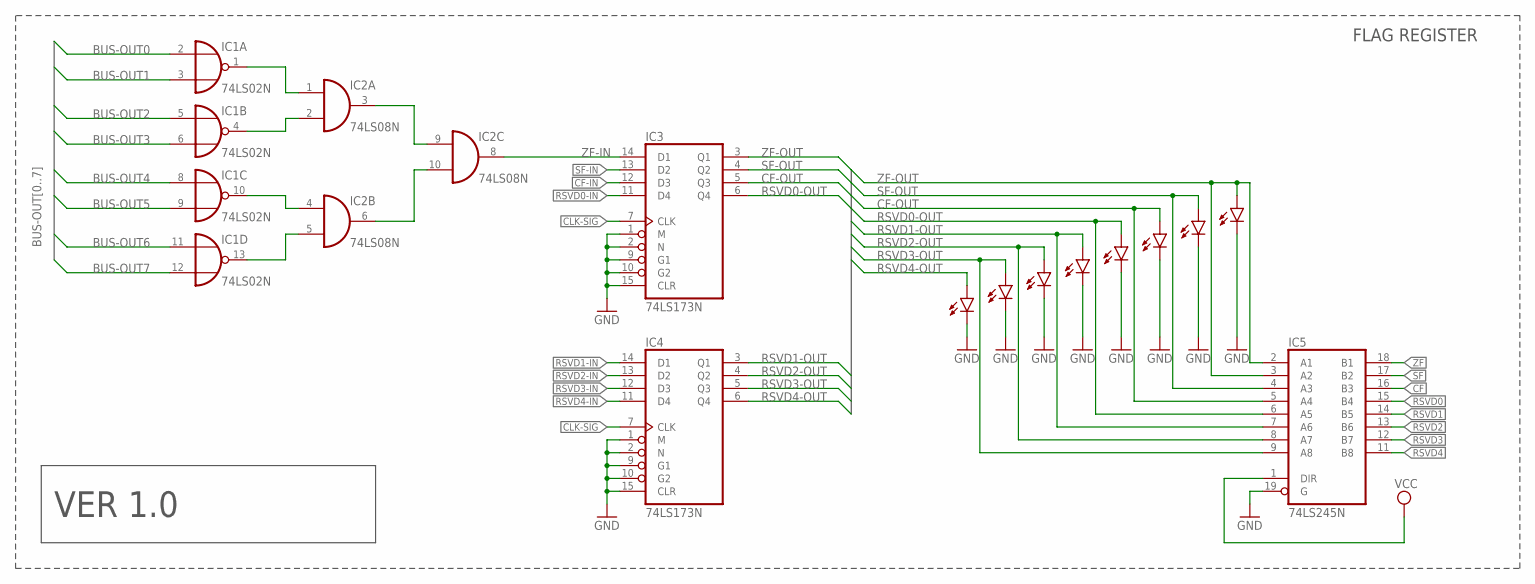
[picture p57: schematic rel-rflag.sch]

Parts:
IC1: 74LS02N; DIL14
IC2: 74LS08N; DIL14
IC3, IC4: 74LS173N; DIL16
IC5: 74LS245N; DIL20
LED1, LED2, LED3, LED4, LED5, LED6, LED7, LED8: LED5MM

Connections:
BUS-OUT0: IC1.2 (I0)
BUS-OUT1: IC1.3 (I1)
BUS-OUT2: IC1.5 (I0)
BUS-OUT3: IC1.6 (I1)
BUS-OUT4: IC1.8 (I0)
BUS-OUT5: IC1.9 (I1)
BUS-OUT6: IC1.11 (I0)
BUS-OUT7: IC1.12 (I1)
CF: IC5.16 (B3)
CF-IN: IC3.12 (D3)
CF-OUT: IC3.5 (Q3), IC5.5 (A4), LED3.A
CLK-SIG: IC3.7 (CLK), IC4.7 (CLK)
GND: IC3.1 (M), IC3.2 (N), IC3.9 (G1), IC3.10 (G2), IC3.15 (CLR), IC4.1 (M), IC4.2 (N), IC4.9 (G1), IC4.10 (G2), IC4.15 (CLR), IC5.19 (G), LED1.K (C), LED2.K (C), LED3.K (C), LED4.K (C), LED5.K (C), LED6.K (C), LED7.K (C), LED8.K (C)
unnamed: IC1.1 (O), IC2.1 (I0)
unnamed: IC1.4 (O), IC2.2 (I1)
unnamed: IC1.10 (O), IC2.4 (I0)
unnamed: IC1.13 (O), IC2.5 (I1)
unnamed: IC2.3 (O), IC2.9 (I0)
unnamed: IC2.6 (O), IC2.10 (I1)
RSVD0: IC5.15 (B4)
RSVD0-IN: IC3.11 (D4)
RSVD0-OUT: IC3.6 (Q4), IC5.6 (A5), LED4.A
RSVD1: IC5.14 (B5)
RSVD1-IN: IC4.14 (D1)
RSVD1-OUT: IC4.3 (Q1), IC5.7 (A6), LED5.A
RSVD2: IC5.13 (B6)
RSVD2-IN: IC4.13 (D2)
RSVD2-OUT: IC4.4 (Q2), IC5.8 (A7), LED6.A
RSVD3: IC5.12 (B7)
RSVD3-IN: IC4.12 (D3)
RSVD3-OUT: IC4.5 (Q3), IC5.9 (A8), LED7.A
RSVD4: IC5.11 (B8)
RSVD4-IN: IC4.11 (D4)
RSVD4-OUT: IC4.6 (Q4), LED8.A
SF: IC5.17 (B2)
SF-IN: IC3.13 (D2)
SF-OUT: IC3.4 (Q2), IC5.4 (A3), LED2.A
VCC: IC5.1 (DIR)
ZF: IC5.18 (B1)
ZF-IN: IC2.8 (O), IC3.14 (D1)
ZF-OUT: IC3.3 (Q1), IC5.2 (A1), IC5.3 (A2), LED1.A

Notes on the sheet:
FLAG REGISTER
VER 1.0
